jedmijares/Battleship-Handheld/Source/printMatrix.c

#include "printMatrix.h"

//x starts at 0 and increments by 7
//y starts at 4 and increments by 6
//text starts at 8,0

const unsigned char empty[] ={
 0x42, 0x4D, 0x8A, 0x00, 0x00, 0x00, 0x00, 0x00, 0x00, 0x00, 0x76, 0x00, 0x00, 0x00, 0x28, 0x00, 0x00, 0x00, 0x06, 0x00, 0x00, 0x00, 0x05, 0x00, 0x00, 0x00, 0x01, 0x00, 0x04, 0x00, 0x00, 0x00,
 0x00, 0x00, 0x14, 0x00, 0x00, 0x00, 0x00, 0x00, 0x00, 0x00, 0x00, 0x00, 0x00, 0x00, 0x00, 0x00, 0x00, 0x00, 0x00, 0x00, 0x00, 0x00, 0x00, 0x00, 0x00, 0x00, 0x00, 0x00, 0x80, 0x00, 0x00, 0x80,
 0x00, 0x00, 0x00, 0x80, 0x80, 0x00, 0x80, 0x00, 0x00, 0x00, 0x80, 0x00, 0x80, 0x00, 0x80, 0x80, 0x00, 0x00, 0x80, 0x80, 0x80, 0x00, 0xC0, 0xC0, 0xC0, 0x00, 0x00, 0x00, 0xFF, 0x00, 0x00, 0xFF,
 0x00, 0x00, 0x00, 0xFF, 0xFF, 0x00, 0xFF, 0x00, 0x00, 0x00, 0xFF, 0x00, 0xFF, 0x00, 0xFF, 0xFF, 0x00, 0x00, 0xFF, 0xFF, 0xFF, 0x00, 0x00, 0x00, 0x00, 0x00, 0x00, 0x00, 0x00, 0x00, 0x00, 0x00,
 0x00, 0x00, 0x00, 0x00, 0x00, 0x00, 0x00, 0x00, 0x00, 0x00, 0xFF,

};
const unsigned char grid[] ={
 0x42, 0x4D, 0xB6, 0x05, 0x00, 0x00, 0x00, 0x00, 0x00, 0x00, 0x76, 0x00, 0x00, 0x00, 0x28, 0x00, 0x00, 0x00, 0x38, 0x00, 0x00, 0x00, 0x30, 0x00, 0x00, 0x00, 0x01, 0x00, 0x04, 0x00, 0x00, 0x00,
 0x00, 0x00, 0x40, 0x05, 0x00, 0x00, 0x00, 0x00, 0x00, 0x00, 0x00, 0x00, 0x00, 0x00, 0x00, 0x00, 0x00, 0x00, 0x00, 0x00, 0x00, 0x00, 0x00, 0x00, 0x00, 0x00, 0x00, 0x00, 0x80, 0x00, 0x00, 0x80,
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
 0x00, 0x00, 0x0F, 0x00, 0x00, 0x00, 0x00, 0x00, 0x00, 0x00, 0x00, 0x00, 0x00, 0x00, 0x00, 0x00, 0x00, 0x00, 0x00, 0x00, 0x00, 0x00, 0x00, 0x00, 0x00, 0x00, 0x00, 0x00, 0x00, 0x00, 0x00, 0x00,
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

};

void printGrid(void){
	Nokia5110_PrintBMP(0,47,grid,1);
	Nokia5110_DisplayBuffer();
}

void print(struct Square in[8][8]){
	for(short i = 0; i<8; i++){
		for(short j = 0; j<8; j++){
			if(in[i][j].isHit && in[i][j].shipID >= 0)
				Nokia5110_PrintBMP(i*7, j*6+4, hit,1);				
			else if(in[i][j].isHit && !(in[i][j].shipID>=0))
				Nokia5110_PrintBMP(i*7, j*6+4, miss,1);
			else
				Nokia5110_PrintBMP(i*7, j*6+4, empty, 1);
		}
	}
}

void select(struct Square in[8][8], short i, short j){
	deselect(in, i+1, j);
	deselect(in, i, j+1);
	deselect(in, i-1, j);
	deselect(in, i, j-1);
	if(in[i][j].isHit && in[i][j].shipID>=0)
		Nokia5110_PrintBMP(i*7, j*6+4, hitOutline,1);				
	else if(in[i][j].isHit && !(in[i][j].shipID >= 0))
		Nokia5110_PrintBMP(i*7, j*6+4, missOutline,1);
	else
		Nokia5110_PrintBMP(i*7, j*6+4, outline, 1);
}

void deselect(struct Square in[8][8], short i, short j){
	if(i>=0 && j>=0){
		if(i<=7 && j<=7){
			if(in[i][j].isHit && in[i][j].shipID>=0)
				Nokia5110_PrintBMP(i*7, j*6+4, hit,1);				
			else if(in[i][j].isHit && !(in[i][j].shipID>=0))
				Nokia5110_PrintBMP(i*7, j*6+4, miss,1);
			else
				Nokia5110_PrintBMP(i*7, j*6+4, empty, 1);
		}
	}
}
	
void winscreen(int hits){
	Nokia5110_PrintBMP(0, 47 , win, 1);
}
